Teufelchen1/XBOX-USB-HUB/imgs/IMG_0317.png

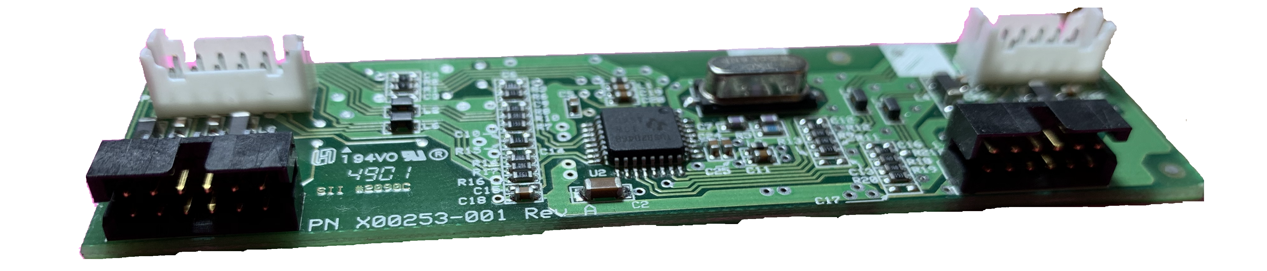
imgs/IMG_0317.png
